zegervdv/HOPDrone/code/drone/kalman.c

/**
 * kalman.c
 * Functions for Unscented Kalman Filtering
 */

#include "kalman.h"
#include <stdlib.h>
#include <math.h>
#include "leds.h"

void kalman_init_weight_factors(float32_t* weight_m, float32_t* weight_c) {
  uint8_t i;

  // Set first indices
  weight_c[0] = WEIGHT_C0;
  weight_m[0] = WEIGHT_M0;

  for (i = 1; i < NR_SIGMAPOINTS; i++) {
    weight_c[i] = WEIGHTS;
    weight_m[i] = WEIGHTS;
  }
}

void kalman_init_position(float32_t* position) {
  uint8_t i;

  for(i = 0; i < DIMENSIONS; i++) {
    position[i] = 0.0;
  }
}

void kalman_init_sigmapoints(float32_t* sigmapoints) {
  uint8_t i;

  for (i = 0; i < DIMENSIONS; i++) {
    sigmapoints[i] = 0;
  }
}

void kalman_init_f_matrix(float32_t* f_matrix) {
  uint8_t i,j;

  for (i = 0; i < DIMENSIONS; i++) {
    for (j = 0; j < DIMENSIONS; j++) {
      if (i == j)
        f_matrix[i*DIMENSIONS + j] = 1;
      else {
        if (j == i + DIMENSIONS/2)
          f_matrix[i*DIMENSIONS + j] = DELTAT;
        else
          f_matrix[i*DIMENSIONS + j] = 0;
      }
    }
  }
}

void kalman_init_g_matrix(float32_t* g_matrix) {
  uint8_t i,j;
  float32_t g_up[(DIMENSIONS/2)*(DIMENSIONS/2)];
  float32_t g_low[(DIMENSIONS/2)*(DIMENSIONS/2)];
  
  kalman_eye_matrix(g_up, DIMENSIONS/2, (DELTAT*DELTAT)/2);
  kalman_eye_matrix(g_low, DIMENSIONS/2, DELTAT);

  for(i = 0; i < DIMENSIONS/2; i++) {
    for(j = 0; j < DIMENSIONS/2; j++) {
      g_matrix[i*(DIMENSIONS/2) + j] = g_up[i*(DIMENSIONS/2) + j];
      g_matrix[(DIMENSIONS/2)*(DIMENSIONS/2) + i*(DIMENSIONS/2) + j] = g_low[i*(DIMENSIONS/2) + j];
    }
  }
}

void kalman_init_dimensional_matrix(float32_t* matrix) {
  kalman_eye_matrix(matrix, DIMENSIONS, 1);
}

void kalman_init_variances(float32_t* variance_u, float32_t* r_matrix) {
  kalman_eye_matrix(variance_u, DIMENSIONS/2, PREDICTION_VAR);
  kalman_eye_matrix(r_matrix, NR_ANCHORS, STD_MEASUREMENT);
}

void kalman_predict(arm_matrix_instance_f32* f_matrix, arm_matrix_instance_f32* g_matrix, position_t* prev_position, arm_matrix_instance_f32* variance, arm_matrix_instance_f32* var_u, arm_matrix_instance_f32* mkmin, arm_matrix_instance_f32* pkmin) {
  int i;
  float32_t interm_f_data[DIMENSIONS*DIMENSIONS], interm_g_data[DIMENSIONS*DIMENSIONS/2];
  float32_t interm_f_data2[DIMENSIONS*DIMENSIONS], interm_g_data2[DIMENSIONS*DIMENSIONS/2];
  float32_t f_matrix_transposed_data[DIMENSIONS*DIMENSIONS], g_matrix_transposed_data[DIMENSIONS*DIMENSIONS];
  arm_matrix_instance_f32 interm_f, interm_g, interm_f2, interm_g2, f_matrix_transposed, g_matrix_transposed;

  // Initialize temporary matrices
  arm_mat_init_f32(&interm_f, DIMENSIONS, DIMENSIONS, interm_f_data);
  arm_mat_init_f32(&interm_g, DIMENSIONS, DIMENSIONS/2, interm_g_data);
  arm_mat_init_f32(&interm_f2, DIMENSIONS, DIMENSIONS, interm_f_data2);
  arm_mat_init_f32(&interm_g2, DIMENSIONS, DIMENSIONS, interm_g_data2);
  arm_mat_init_f32(&f_matrix_transposed, DIMENSIONS, DIMENSIONS, f_matrix_transposed_data);
  arm_mat_init_f32(&g_matrix_transposed, DIMENSIONS/2, DIMENSIONS, g_matrix_transposed_data);

  // Calculate mkmin
  arm_mat_mult_f32(f_matrix, prev_position, mkmin);

  // Calculate first intermediate results
  arm_mat_mult_f32(f_matrix, variance, &interm_f);
  arm_mat_mult_f32(g_matrix, var_u, &interm_g);

  // Transpose F and G
  arm_mat_trans_f32(f_matrix, &f_matrix_transposed);
  arm_mat_trans_f32(g_matrix, &g_matrix_transposed);

  // Calculate second intermediate results
  arm_mat_mult_f32(&interm_f, &f_matrix_transposed, &interm_f2);
  arm_mat_mult_f32(&interm_g, &g_matrix_transposed, &interm_g2);

  // Sum up
  arm_mat_add_f32(&interm_f2, &interm_g2, pkmin);
}

void kalman_update_sigmapoints(position_t* sigmapoints, position_t mkmin, arm_matrix_instance_f32* pkmin) {
  uint8_t i,j;
  arm_matrix_instance_f32 root;
  float32_t root_data[DIMENSIONS * DIMENSIONS] = {0};

  arm_mat_init_f32(&root, DIMENSIONS, DIMENSIONS, root_data);

  // Calculate the root of the variance matrix using Cholesky Decomposition
  cholesky(pkmin, &root);

  arm_mat_scale_f32(&root, ROOT_CHOL, &root);

  // First sigmapoint is mkmin
  for(i = 0; i < DIMENSIONS; i++) {
    sigmapoints[0].pData[i] = mkmin.pData[i];
  }

  for(i = 0; i < DIMENSIONS; i++) {
    for(j = 0; j < DIMENSIONS; j++) {
      sigmapoints[i + 1].pData[j] = mkmin.pData[j] + root.pData[i + (j * DIMENSIONS)];
    }

    for(j = 0; j < DIMENSIONS; j++) {
      sigmapoints[i + DIMENSIONS + 1].pData[j] = mkmin.pData[j] - root.pData[i + (j * DIMENSIONS)];
    }
  }
}

void kalman_measurement_update(arm_matrix_instance_f32* z_matrix, float32_t anchors[][4], position_t* sigmapoints, arm_matrix_instance_f32* weight_m, arm_matrix_instance_f32* weight_c, arm_matrix_instance_f32* r_matrix, arm_matrix_instance_f32* pkmin, position_t* mk, arm_matrix_instance_f32* pk) {
  uint8_t i,j;
  arm_matrix_instance_f32 mu;
  arm_matrix_instance_f32 cov, var;
  arm_matrix_instance_f32 vector_y, vector_z, vector_output;
  arm_matrix_instance_f32 temp_cov, temp_var, temp_dim_anch;
  arm_matrix_instance_f32 distance_anchors;
  arm_matrix_instance_f32 pkmin_trans;
  arm_matrix_instance_f32 interm_pk;

  float32_t mu_data[NR_ANCHORS] = {0};
  float32_t cov_data[DIMENSIONS * NR_ANCHORS] = {0};
  float32_t var_data[NR_ANCHORS * NR_ANCHORS] = {0};
  float32_t vector_y_data[DIMENSIONS];
  float32_t vector_z_data[NR_ANCHORS];
  float32_t vector_output_data[NR_ANCHORS];
  float32_t temp_cov_data[DIMENSIONS * NR_ANCHORS];
  float32_t temp_dim_anch_data[DIMENSIONS * NR_ANCHORS];
  float32_t temp_var_data[NR_ANCHORS * NR_ANCHORS];
  float32_t distance_anchors_data[NR_ANCHORS];
  float32_t pkmin_trans_data[DIMENSIONS*DIMENSIONS];
  float32_t interm_pk_data[DIMENSIONS*DIMENSIONS];

  float32_t x_sq, y_sq, z_sq;

  arm_status status;

  arm_mat_init_f32(&mu, NR_ANCHORS, 1, mu_data);
  arm_mat_init_f32(&cov, DIMENSIONS, NR_ANCHORS, cov_data);
  arm_mat_init_f32(&var, NR_ANCHORS, NR_ANCHORS, var_data);
  arm_mat_init_f32(&vector_y, DIMENSIONS, 1, vector_y_data);
  arm_mat_init_f32(&vector_z, NR_ANCHORS, 1, vector_z_data);
  arm_mat_init_f32(&vector_output, 1, NR_ANCHORS, vector_output_data);
  arm_mat_init_f32(&temp_cov, DIMENSIONS, NR_ANCHORS, temp_cov_data);
  arm_mat_init_f32(&temp_dim_anch, NR_ANCHORS, DIMENSIONS, temp_dim_anch_data);
  arm_mat_init_f32(&temp_var, NR_ANCHORS, NR_ANCHORS, temp_var_data);
  arm_mat_init_f32(&distance_anchors, NR_ANCHORS, 1, distance_anchors_data);
  arm_mat_init_f32(&pkmin_trans, DIMENSIONS, DIMENSIONS, pkmin_trans_data);
  arm_mat_init_f32(&interm_pk, DIMENSIONS, DIMENSIONS, interm_pk_data);

  for(i = 0; i < NR_SIGMAPOINTS; i++) {
    for(j = 0; j < NR_ANCHORS; j++) {
      float32_t result;
      x_sq = (sigmapoints[i].pData[0] - anchors[j][0]) * (sigmapoints[i].pData[0] - anchors[j][0]);
      y_sq = (sigmapoints[i].pData[1] - anchors[j][1]) * (sigmapoints[i].pData[1] - anchors[j][1]);
      z_sq = (sigmapoints[i].pData[2] - anchors[j][2]) * (sigmapoints[i].pData[2] - anchors[j][2]);
      arm_sqrt_f32(x_sq + y_sq + z_sq, &result);
      z_matrix->pData[j*NR_SIGMAPOINTS + i] = result; 
    }
  }
  // Collect distances measured
  for(i = 0; i < NR_ANCHORS; i++) {
    distance_anchors.pData[i] = anchors[i][3];
  }

  // Calculate mu vector
  status = arm_mat_mult_f32(z_matrix, weight_m, &mu);

  // Calculate covariance matrix
  for(i = 0; i < NR_SIGMAPOINTS; i++) {
    // Select vector Y
    for(j = 0; j < DIMENSIONS; j++)
      vector_y.pData[j] = sigmapoints[i].pData[j];
    // Select vector Z
    for(j = 0; j < NR_ANCHORS; j++)
      vector_z.pData[j] = z_matrix->pData[i + j * NR_SIGMAPOINTS];
    arm_mat_sub_f32(&vector_y, &sigmapoints[0], &vector_y);
    arm_mat_sub_f32(&vector_z, &mu, &vector_z);

    arm_mat_trans_f32(&vector_z, &vector_output);

    arm_mat_mult_f32(&vector_y, &vector_output, &temp_cov);
    arm_mat_scale_f32(&temp_cov, weight_c->pData[i], &temp_cov);

    arm_mat_mult_f32(&vector_z, &vector_output, &temp_var);
    arm_mat_scale_f32(&temp_var, weight_c->pData[i], &temp_var);

    arm_mat_add_f32(&cov, &temp_cov, &cov);
    arm_mat_add_f32(&var, &temp_var, &var);
  }

  
  arm_mat_add_f32(&var, r_matrix, &temp_var);
  // Reuse var to store the inverse
  status = arm_mat_inverse_f32(&temp_var, &var);

  // temp_cov is used to store K matrix
  status = arm_mat_mult_f32(&cov, &var, &temp_cov);

  // Reuse distance_anchors to store result
  status = arm_mat_sub_f32(&distance_anchors, &mu, &distance_anchors);
  // Reuse vector_y
  status = arm_mat_mult_f32(&temp_cov, &distance_anchors, &vector_y);

  // Result for mk
  status = arm_mat_add_f32(&sigmapoints[0], &vector_y, mk);

  // cov holds result of K * (var + R)
  arm_mat_mult_f32(&temp_cov, &temp_var, &cov);
  arm_mat_trans_f32(&temp_cov, &temp_dim_anch);
  arm_mat_mult_f32(&cov, &temp_dim_anch, &interm_pk);

  // Result for Pk
  arm_mat_sub_f32(pkmin, &interm_pk, pk);
  arm_mat_trans_f32(pk, &pkmin_trans);
  arm_mat_add_f32(pk, &pkmin_trans, pk);
  arm_mat_scale_f32(pk, 0.5, pk);

}

void cholesky(arm_matrix_instance_f32* matrix, arm_matrix_instance_f32* output) {
  int8_t i,j,k;
  float32_t diag[DIMENSIONS]; 

  for(i = 0; i < DIMENSIONS*DIMENSIONS; i++)
    output->pData[i] = matrix->pData[i];

  for(j=0;j<matrix->numRows;j++) {
    diag[j] = output->pData[matrix->numRows*j + j];
  }

  for(j=0;j<matrix->numRows;j++) {
    for(k=0;k<j;k++) {
      diag[j] -= output->pData[matrix->numRows*k + j] * output->pData[matrix->numRows*k + j];
    }
    float32_t root;
    arm_status stat;
    stat = arm_sqrt_f32(diag[j], &root);
    diag[j] = root;

    for (i=j+1; i<matrix->numRows; i++) {
      for (k=0; k<j; k++) {
        output->pData[matrix->numRows*j + i] -= output->pData[matrix->numRows*k + i] * output->pData[matrix->numRows * k + j];
      }
      output->pData[matrix->numRows*j + i] /= diag[j];
    }
  }

  for(i=0;i<DIMENSIONS;i++) {
    output->pData[i*DIMENSIONS + i] = diag[i];
  }
}

void kalman_eye_matrix(float32_t* array, uint8_t size, float32_t value) {
  uint8_t i,j;

  for (i = 0; i < size; i++) {
    for (j = 0; j < size; j++) {
      if (i == j)
        array[i * size + j] = value;
      else
        array[i * size + j] = 0;
    }
  }
}
